TKOT/HanChan-FCU/3D打印模型/高度旋钮部分/连杆.stl

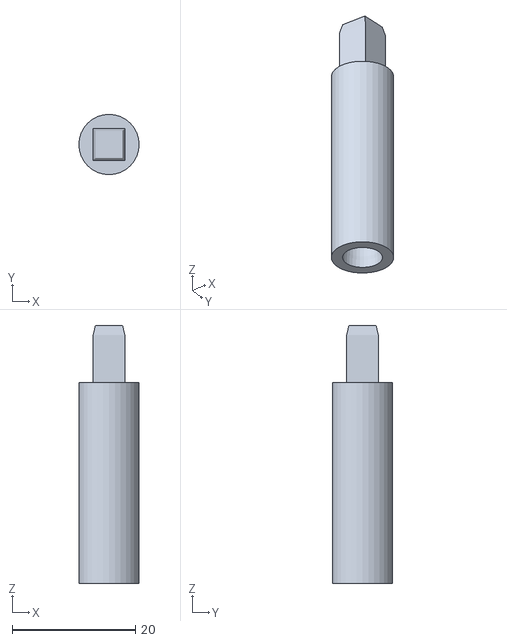
[picture p27: CAD file, 2024-06-28]
3D打印模型/高度旋钮部分/连杆.stl
9.80 x 9.80 x 41.9
