TKOT/HanChan-FCU/3D打印模型/高度选择按钮.stl

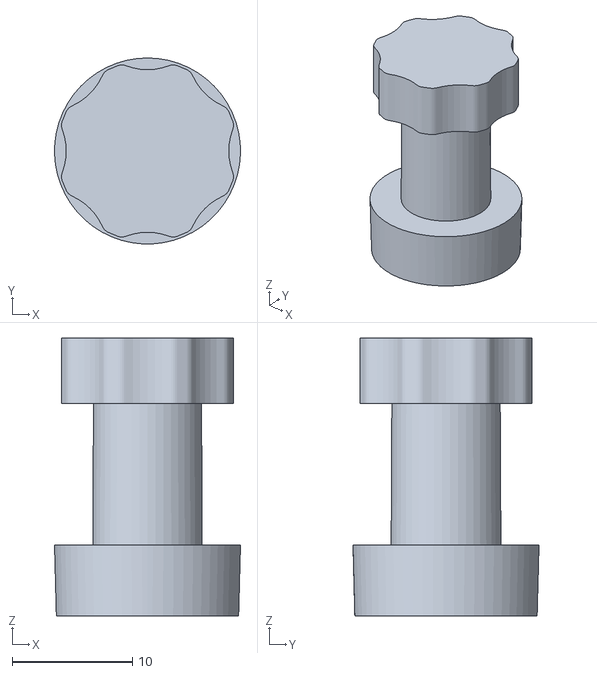
[picture p28: CAD file, 2024-06-28]
3D打印模型/高度选择按钮.stl
15.4 x 15.5 x 23.1
