TKOT/HanChan-FCU/3D打印模型/推拉内壳.stl

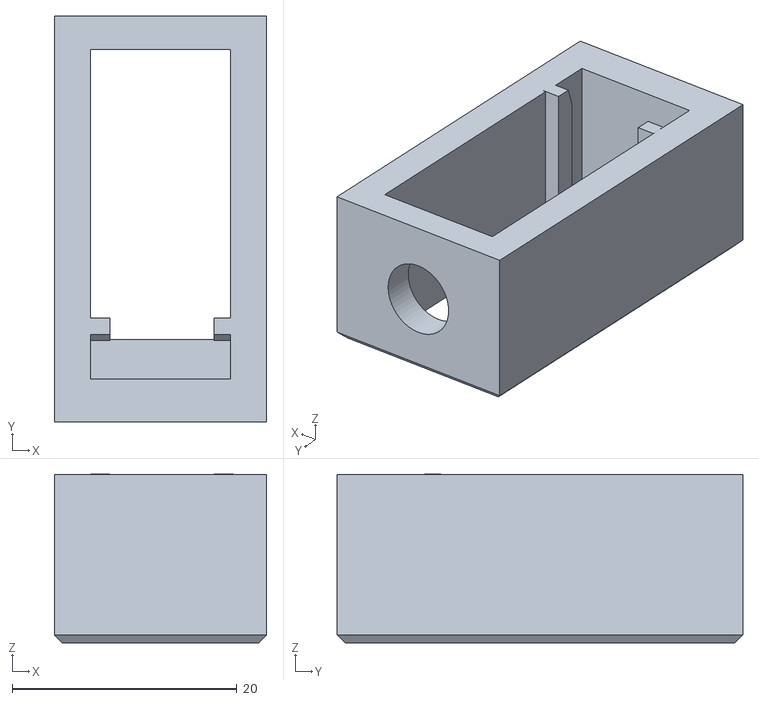
[picture p29: CAD file, 2024-06-28]
3D打印模型/推拉内壳.stl
18.9 x 36.2 x 15.0
