TKOT/HanChan-FCU/3D打印模型/高度旋钮部分/100-1000选择旋帽.stl

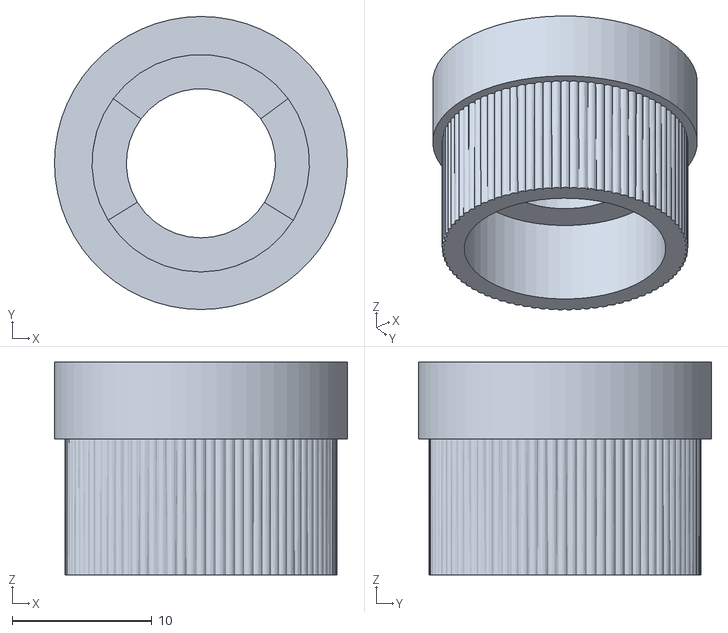
[picture p30: CAD file, 2024-06-28]
3D打印模型/高度旋钮部分/100-1000选择旋帽.stl
21.0 x 21.0 x 15.3
