TKOT/HanChan-FCU/3D打印模型/主面板.stl

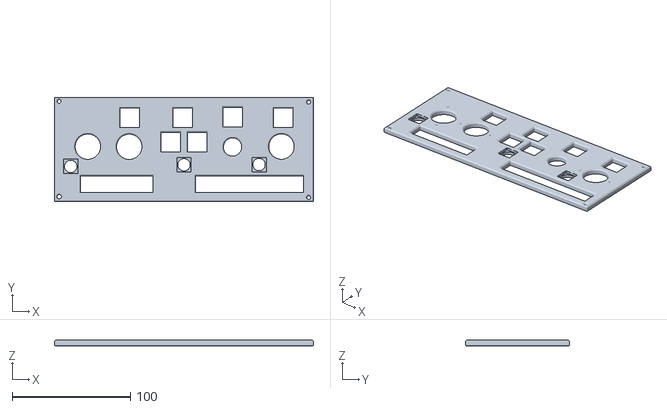
[picture p31: CAD file, 2024-06-28]
3D打印模型/主面板.stl
219.0 x 88.0 x 5.00
