TKOT/HanChan-FCU/3D打印模型/航向 按钮.stl

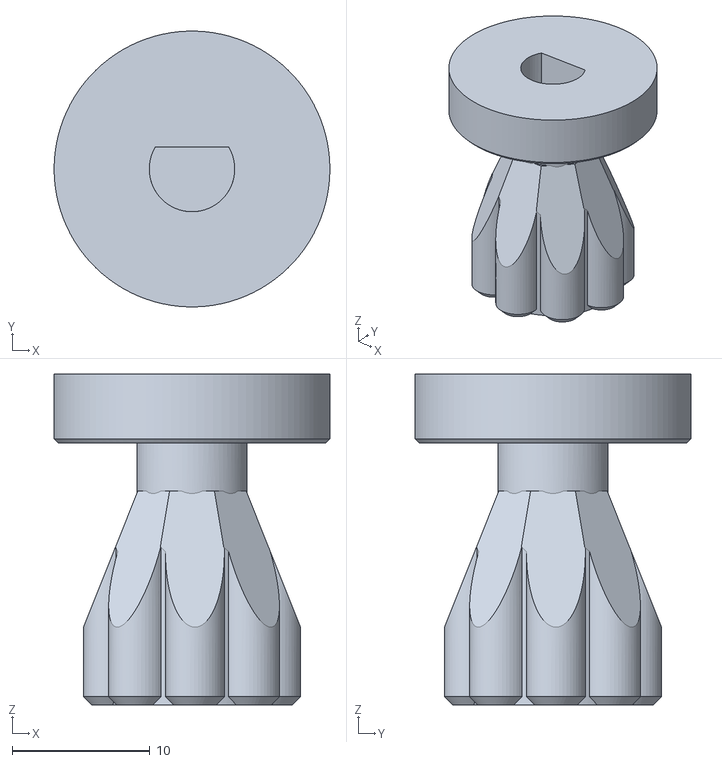
[picture p32: CAD file, 2024-06-28]
3D打印模型/航向 按钮.stl
20.0 x 20.0 x 24.0
