TKOT/HanChan-FCU/3D打印模型/航向按钮 圆形版本.stl

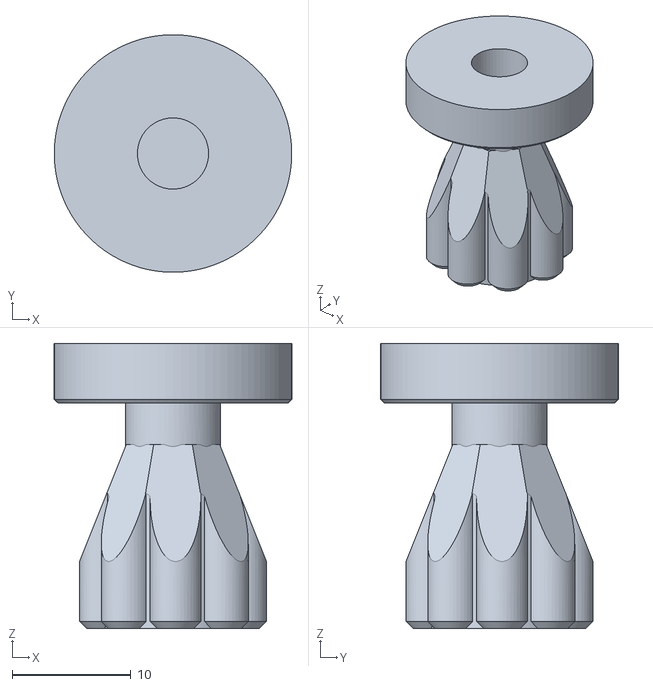
[picture p33: CAD file, 2024-06-28]
3D打印模型/航向按钮 圆形版本.stl
20.0 x 20.0 x 24.0
